lhondareyte/SMART-PSU/firmware/power-button.c

/*
 * Copyright (c)2018, Luc Hondareyte
 * All rights reserved.
 * 
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
 */
/*
 * POWER BUTTON - AVR Version
 *
 * Copyright (c)2018, Luc Hondareyte
 * All rights reserved.
 *
 * $Id$
 */

#include "power-button.h"
#include <avr/io.h>
#include <stdlib.h>
#include <avr/interrupt.h>
#include <stdint.h>
#include <util/delay.h>
#include <avr/sleep.h>
#include <avr/power.h>

// Time to wait operating systeme
#define STARTUP_TIMEOUT 20
#define SHUTDOWN_TIMEOUT 20

inline void SetupHardware(void ) {

	// Set ports direction
	D_PORT=0x00;
	setBit(D_PORT,LED);
	setBit(D_PORT,PWR);
	// Pullup resistor on button pin
	setBit(PORT,BUTTON);

	// Active INT0
#if defined (__AVR_ATmega328P__)
	clearBit(EICRA,ISC00);
	clearBit(EICRA,ISC01);
	setBit(EIMSK,INT0);
#else
#warning "No timer defined"
#endif
	sei();
}

uint8_t board_is_on=0;
uint8_t os_is_active=0;

uint8_t volatile seconds=0;
uint16_t volatile _ms=0x0000;

#if defined (__AVR_ATtiny13A__) || defined (__AVR_ATtiny13__)
ISR (TIM0_OVF_vect) {
#else
ISR (TIMER0_OVF_vect) {
#endif
	_ms++;
	if ( _ms == 1000 ) {
		_ms=0;
		seconds++;
	}
}

ISR (INT0_vect) {
	// Just Wake-up CPU
}

inline void heartbeat(void) {
}

inline void startTimer(void) {
}

inline void stopTimer(void) {
}

inline void waitForStartup(int t) {
}

inline void waitForShutdown(int t) {
}

uint8_t powerOn(void){
	uint8_t rc=0;
	//
	// Wait for key pressed
	//
	loop_until_bit_is_clear(IPORT,BUTTON);
	switchOn();
	_delay_ms(200);
	startTimer();
	//
	// Allow immediate power off within 3 seconds after power on
	//
	while ( seconds <= 3 ) {
		if ( bit_is_set (PORT,BUTTON) ) {
			switchOff();
			_delay_ms(200);
			rc=1;
			break;
		}
	}
	stopTimer();
	return(rc);
}

int main(void){

	SetupHardware();
	//
	// Power-down configuration
	set_sleep_mode(SLEEP_MODE_PWR_DOWN);
	switchOff();
	board_is_on=NO;
	os_is_active=NO;
	while (1) {
		sleep_enable();
		sleep_mode();
		sleep_disable();
		/* 
		   ...zzzzzzzzzzzz
		   Waiting for INT0.
		 */

		 /*
		  * disable INT0
		  */
#if defined (__AVR_ATmega328P__)
		clearBit(EIMSK,INT0);
#endif
		if (board_is_on) {
			if (os_is_active) {
				waitForShutdown(SHUTDOWN_TIMEOUT);
			}
			switchOff();
			board_is_on=NO;
		}
		else {
			switchOn();
			board_is_on=YES;
			//waitForStartup(STARTUP_TIMEOUT);
			//switchOff();
			//board_is_on=NO;
		}
		/*
		 *  Debounce
		 */
		loop_until_bit_is_set(IPORT,BUTTON);
		_delay_ms(100);
		/*
		 * Re-enable INT0
		 */
#if defined (__AVR_ATmega328P__)
		setBit(EIMSK,INT0);
#endif
	}
}
